tmc-digiboys/TMC-LZ210-Command-Station-PCB/docs/images-nFault/drv8874_00_inrush_zoom.png

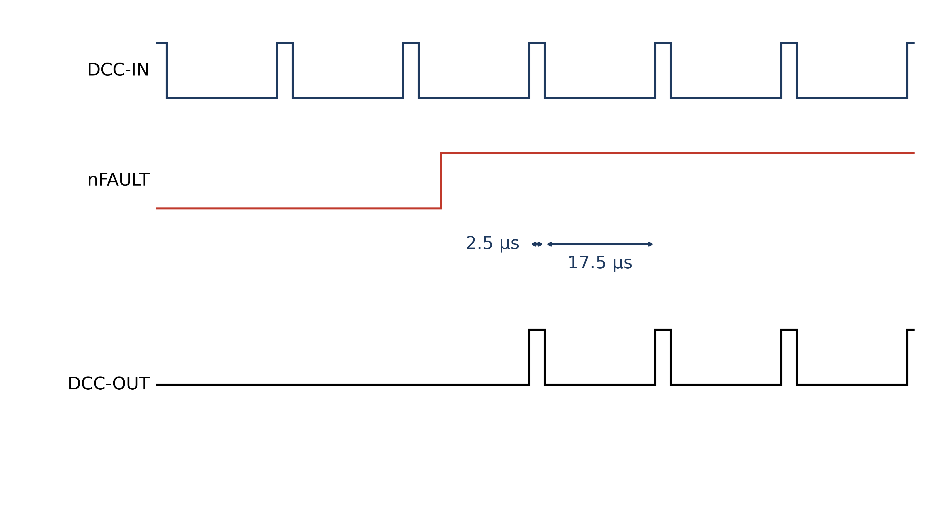
docs/images-nFault/drv8874_00_inrush_zoom.png
