tmc-digiboys/TMC-LZ210-Command-Station-PCB/docs/images/DCC-CommandStation-LZ210-TMC.png

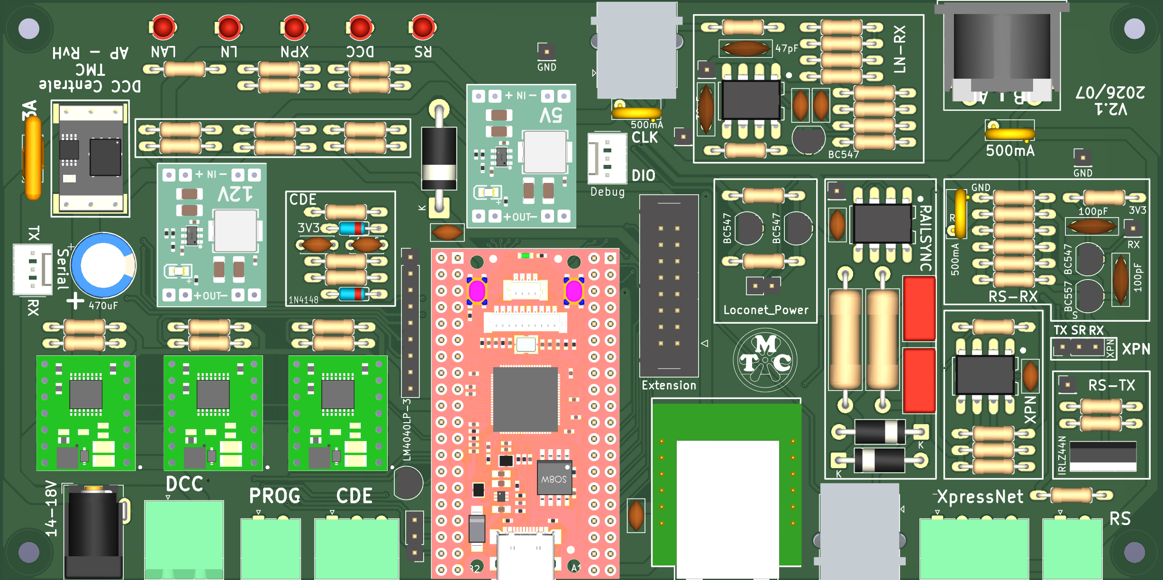
docs/images/DCC-CommandStation-LZ210-TMC.png
