tmc-digiboys/TMC-LZ210-Command-Station-PCB/docs/images/PCB-Bottom.png

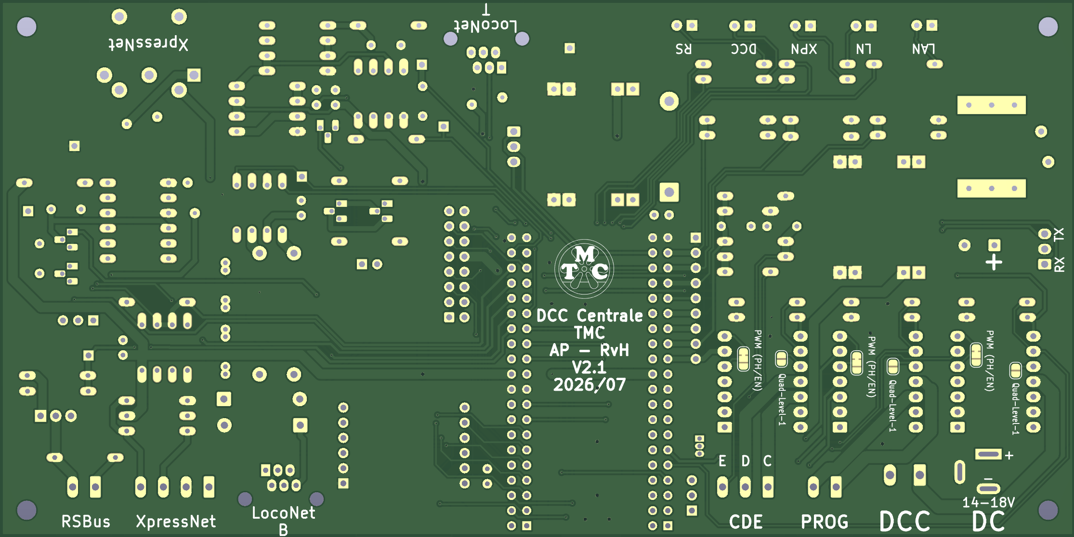
docs/images/PCB-Bottom.png
